htl-leo-itp-25-27-4-5BHITM/SmartSeat/project/C_Pi_Movement/C_PI/WLANConf.h

#ifndef WIFI_NAME
#define WIFI_NAME std::getenv("WIFI_NAME") 
#endif

#ifndef WIFI_PASSWORDV
#define WIFI_PASSWORDV std::getenv("WIFI_PASSWORDV") 
#endif

#ifndef MQTT_SERVERV
#define MQTT_SERVERV std::getenv("MQTT_SERVERV") 
#endif

#ifndef MQTT_USERNAMEV
#define MQTT_USERNAMEV std::getenv("MQTT_USERNAMEV")
#endif

#ifndef MQTT_PASSWORDV
#define MQTT_PASSWORDV std::getenv("MQTT_PASSWORDV")
#endif // !MQTT_PASSWORDV
